carlgoshert/PC_Cartridge_System/docs/schematics/pcart_reader/PCB_PCB1.png

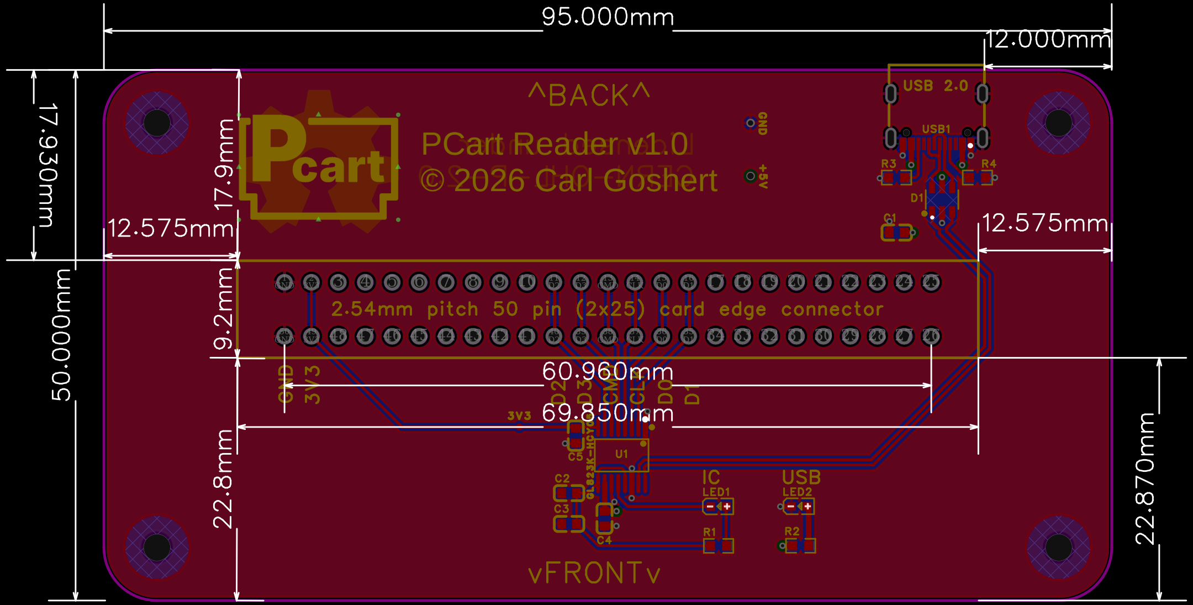
docs/schematics/pcart_reader/PCB_PCB1.png
