carlgoshert/PC_Cartridge_System/docs/templates/labels/slim_label_template.png

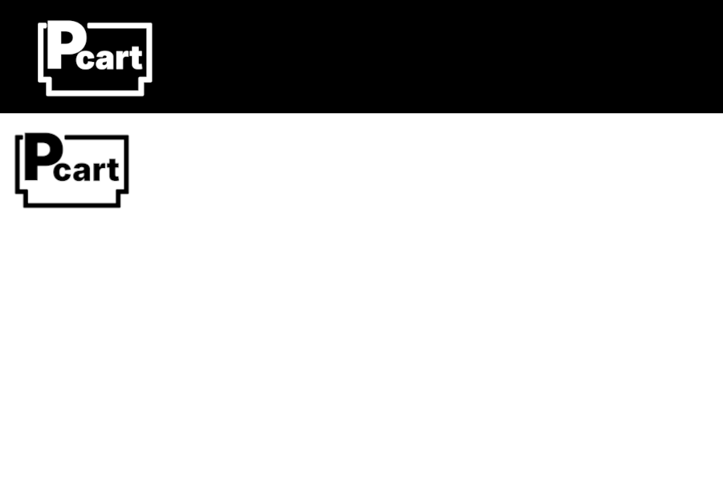
docs/templates/labels/slim_label_template.png
