carlgoshert/PC_Cartridge_System/docs/templates/labels/standard_label_template.png

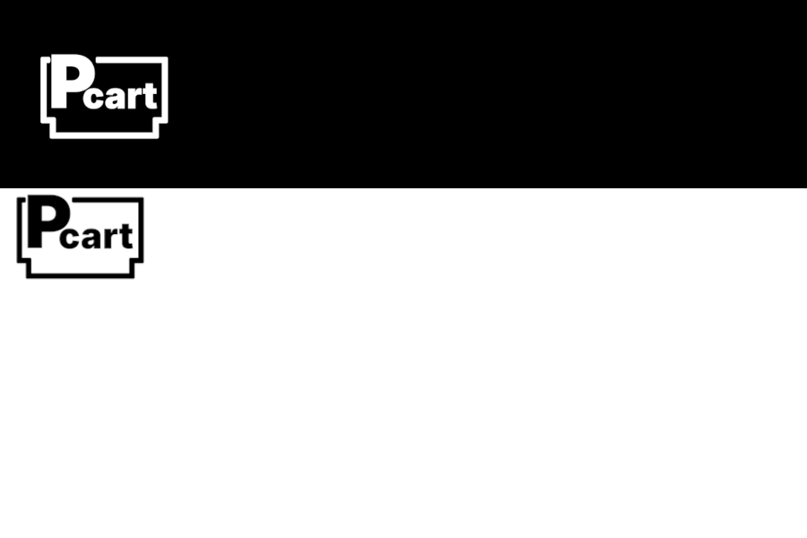
docs/templates/labels/standard_label_template.png
