carlgoshert/PC_Cartridge_System/images/wiki/br1.jpg

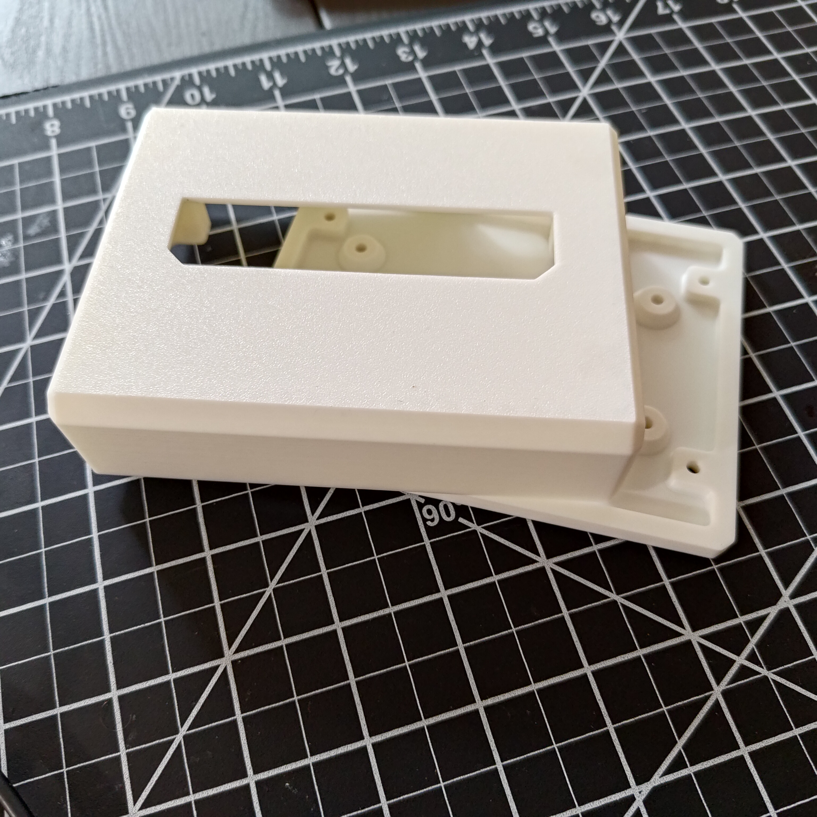
images/wiki/br1.jpg
