carlgoshert/PC_Cartridge_System/images/wiki/br2.jpg

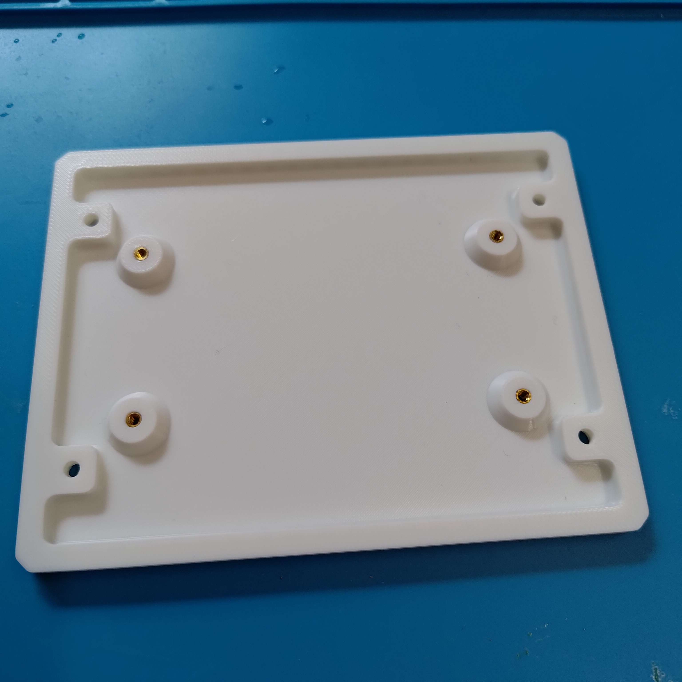
images/wiki/br2.jpg
