carlgoshert/PC_Cartridge_System/images/wiki/br3.jpg

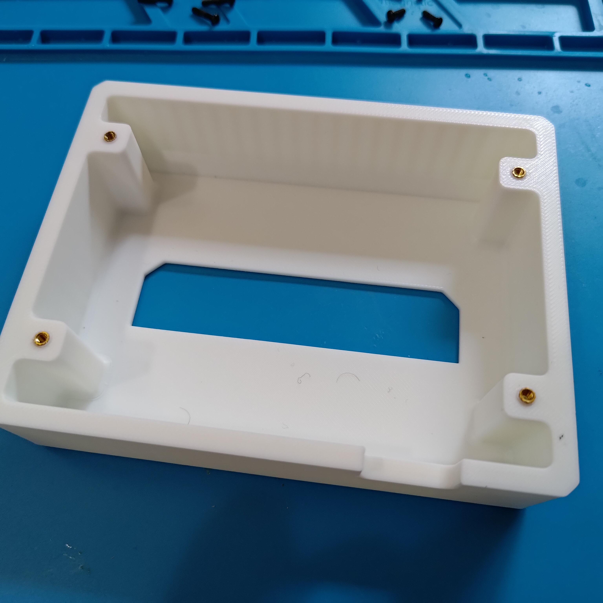
images/wiki/br3.jpg
