carlgoshert/PC_Cartridge_System/images/wiki/br4.jpg

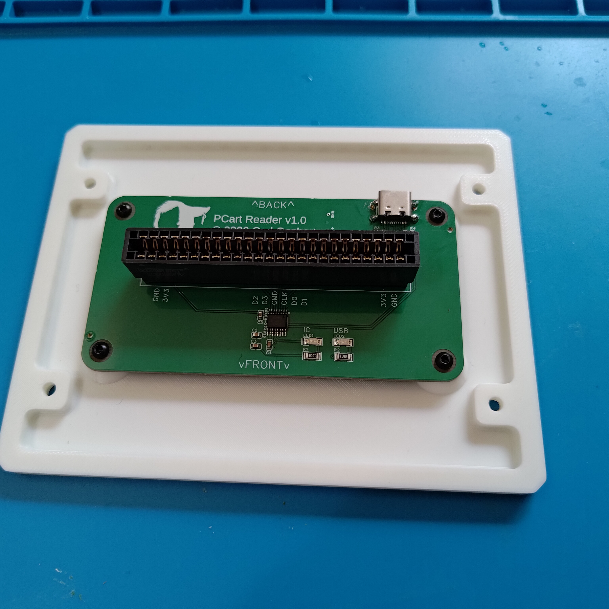
images/wiki/br4.jpg
