carlgoshert/PC_Cartridge_System/images/wiki/br5.jpg

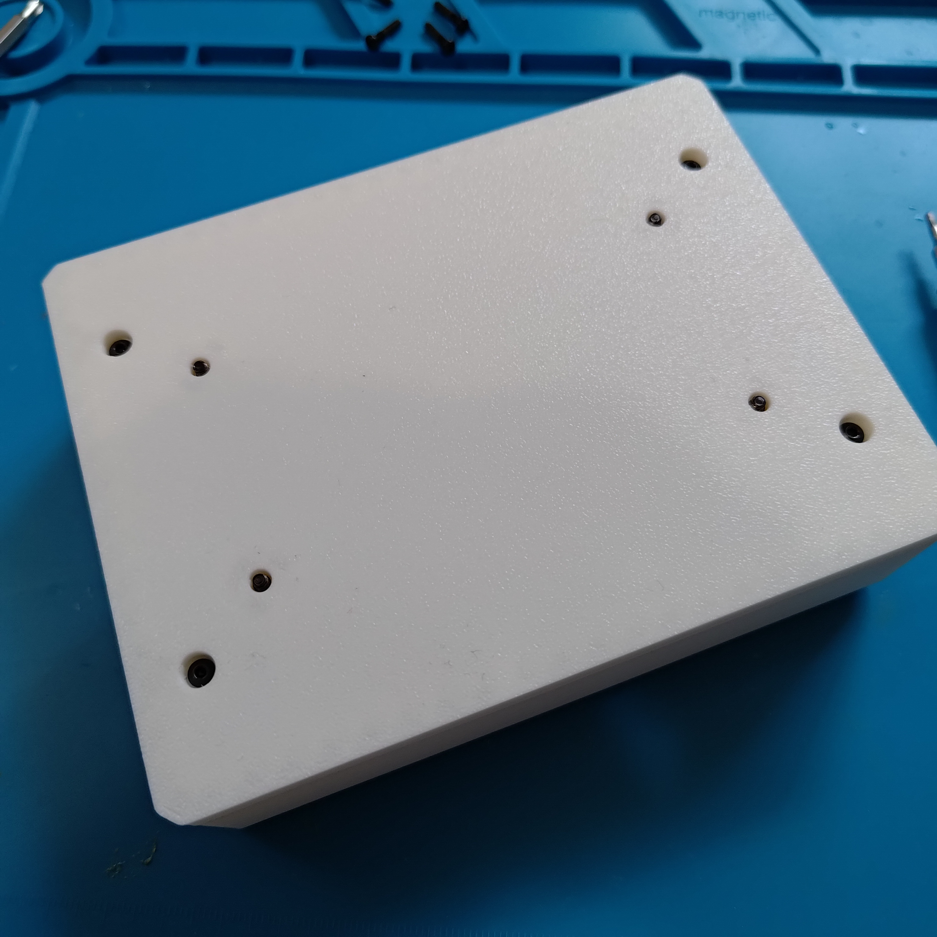
images/wiki/br5.jpg
