carlgoshert/PC_Cartridge_System/images/wiki/br6.jpg

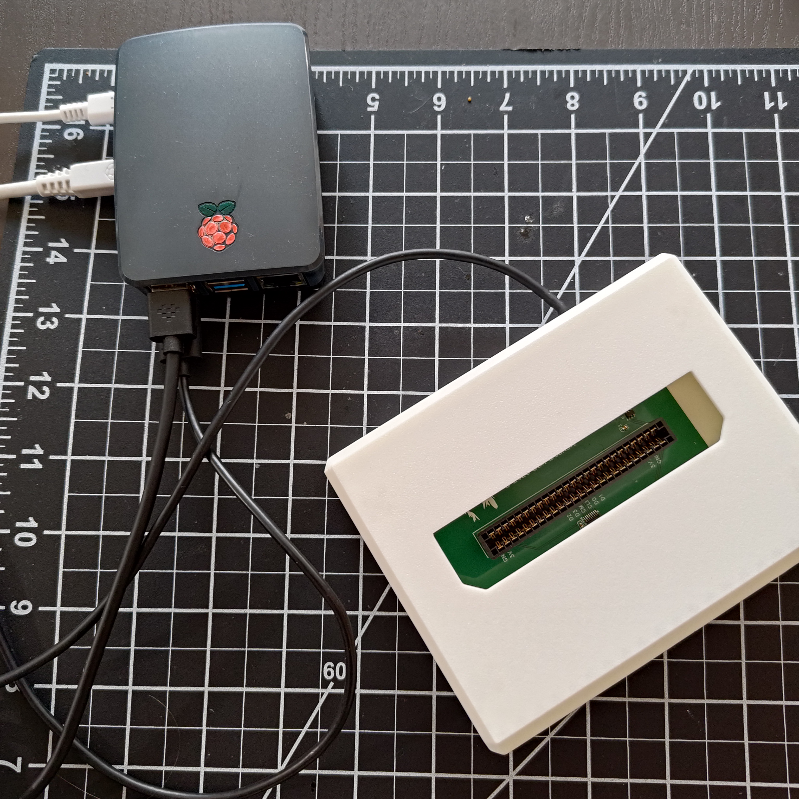
images/wiki/br6.jpg
