carlgoshert/PC_Cartridge_System/images/wiki/img1.jpg

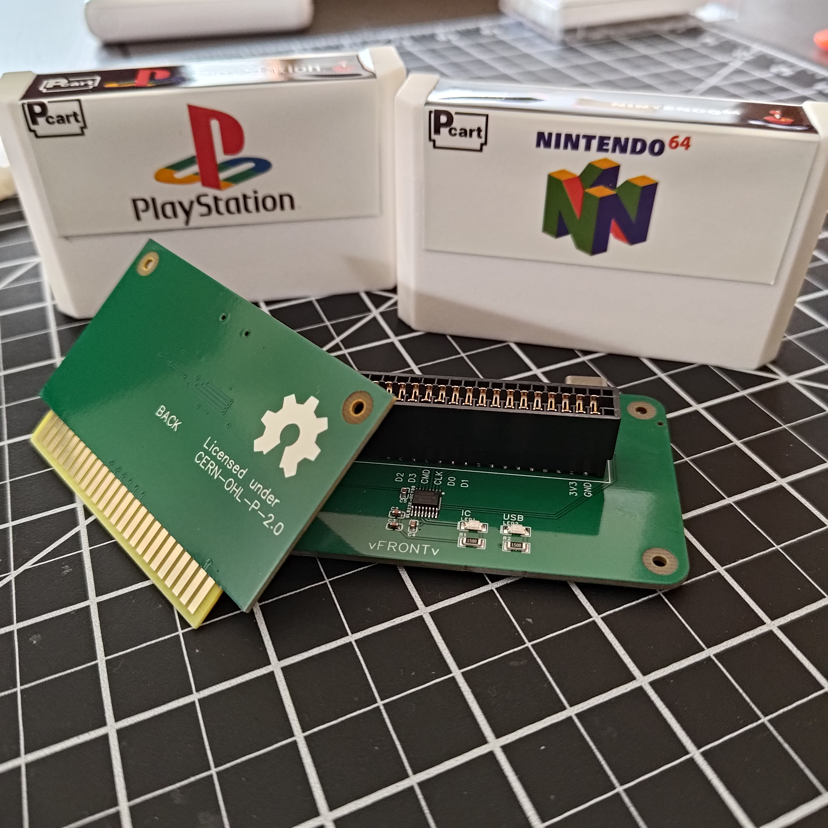
images/wiki/img1.jpg
