carlgoshert/PC_Cartridge_System/images/wiki/tool1.jpg

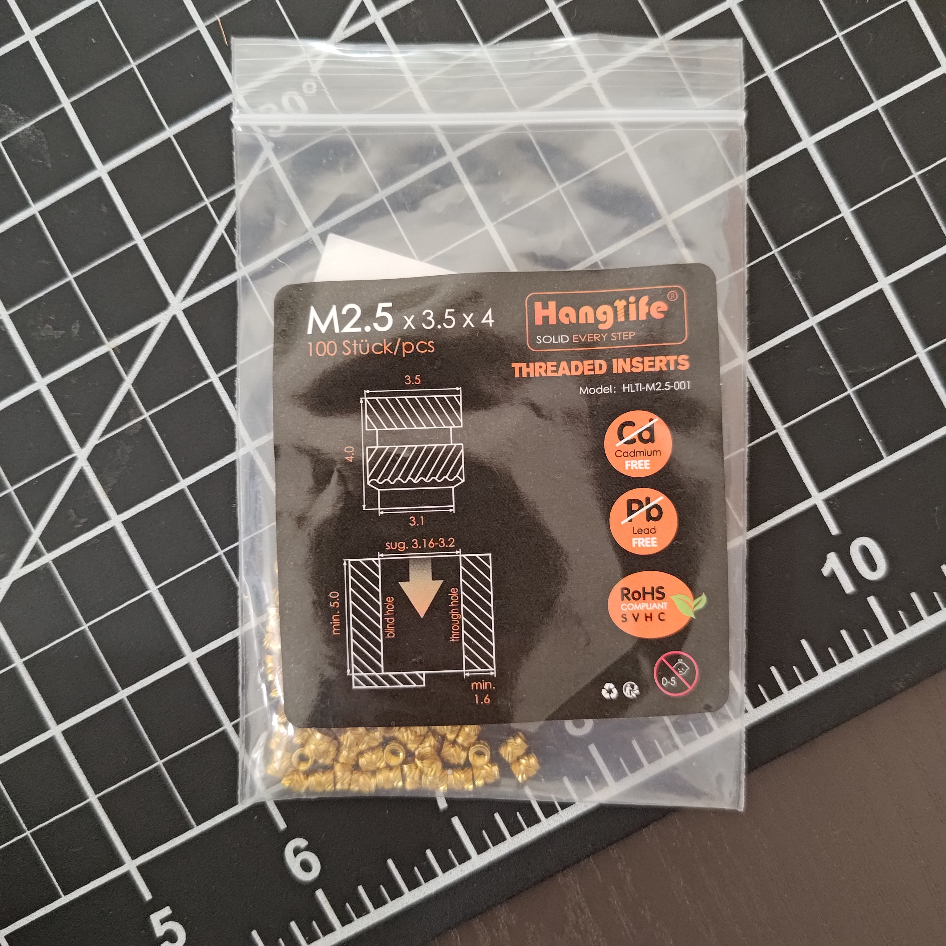
images/wiki/tool1.jpg
