carlgoshert/PC_Cartridge_System/images/wiki/tool2.jpg

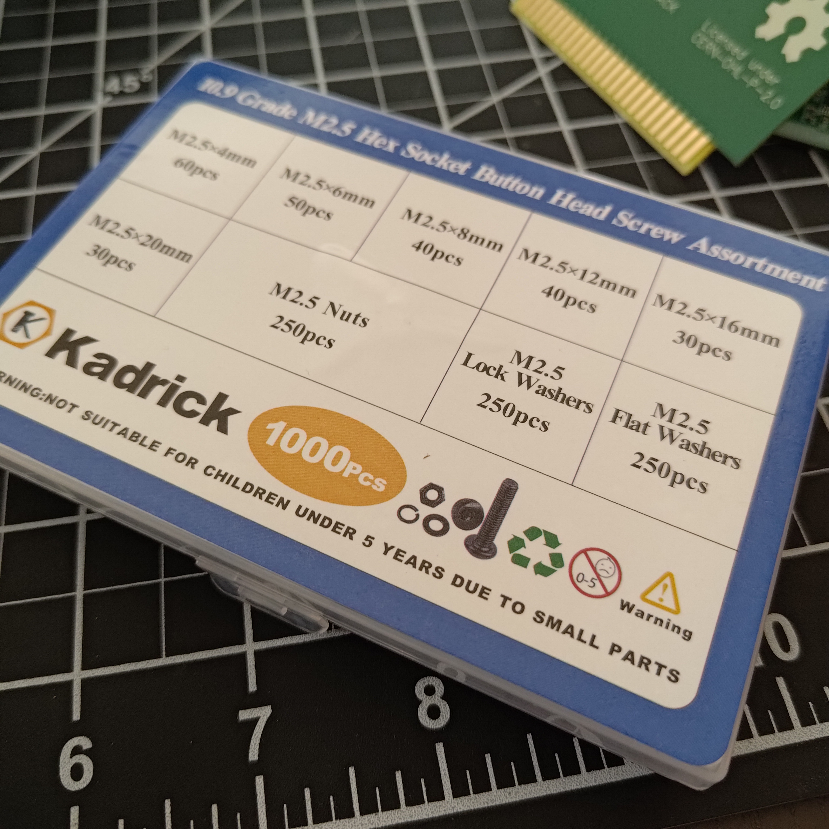
images/wiki/tool2.jpg
