carlgoshert/PC_Cartridge_System/images/wiki/tool3.jpg

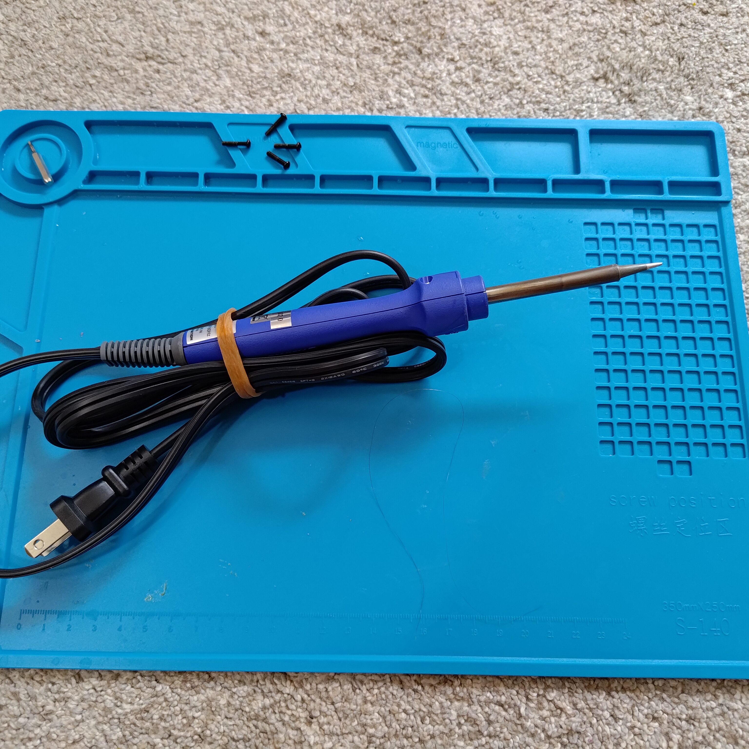
images/wiki/tool3.jpg
